kholia/PDX-Plus-Plus/screenshots/SA-On-Random-Wire-In-Balcony-Screenshot_2022-12-01_08-14-44.png

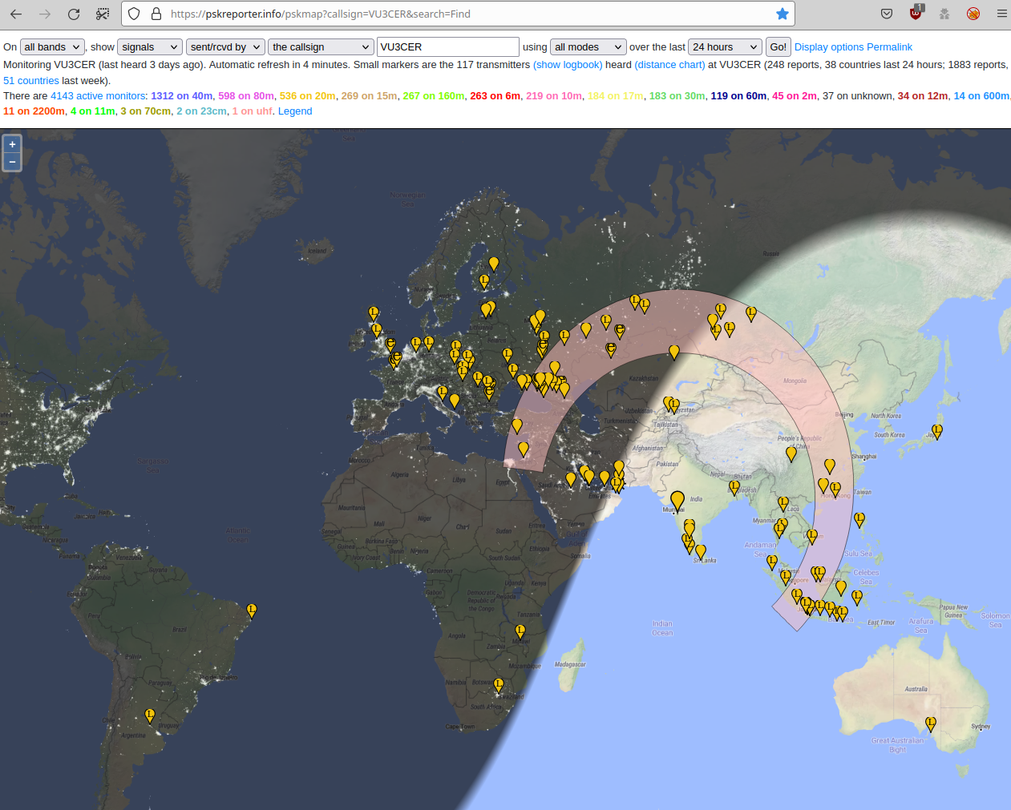
screenshots/SA-On-Random-Wire-In-Balcony-Screenshot_2022-12-01_08-14-44.png
