kholia/PDX-Plus-Plus/screenshots/Screenshot_2022-11-28_12-23-08.png

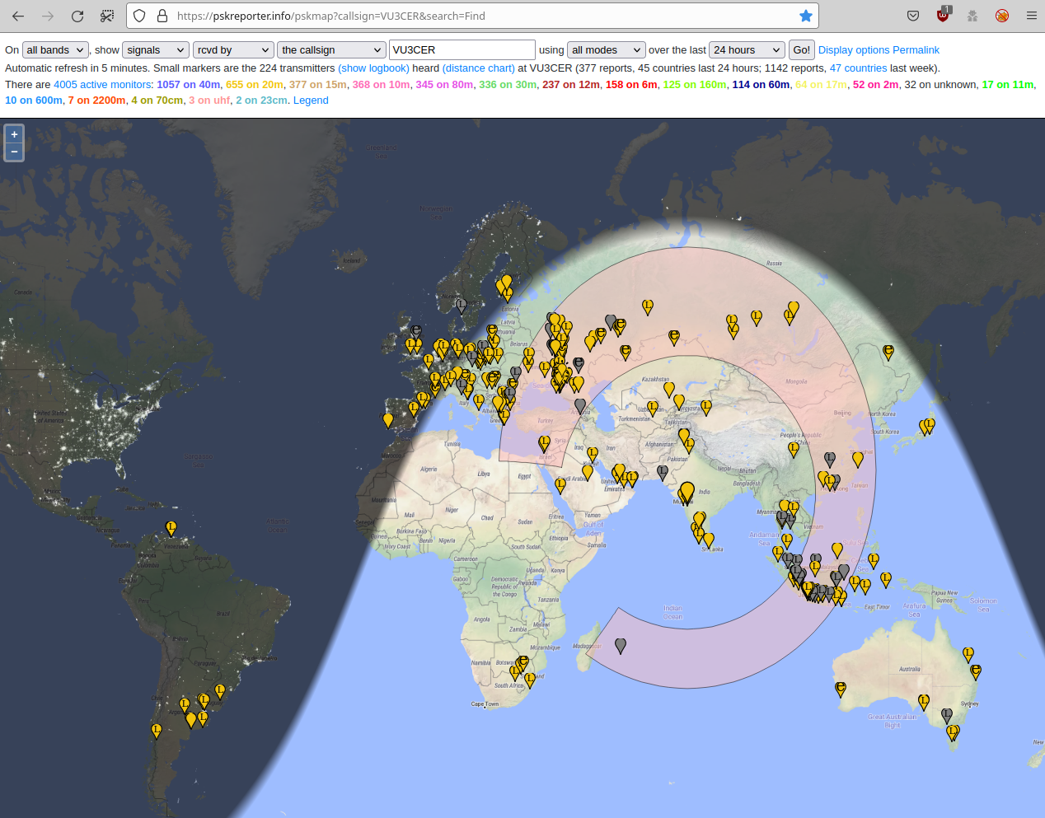
screenshots/Screenshot_2022-11-28_12-23-08.png
