kholia/PDX-Plus-Plus/screenshots/Screenshot_2022-11-28_17-31-01.png

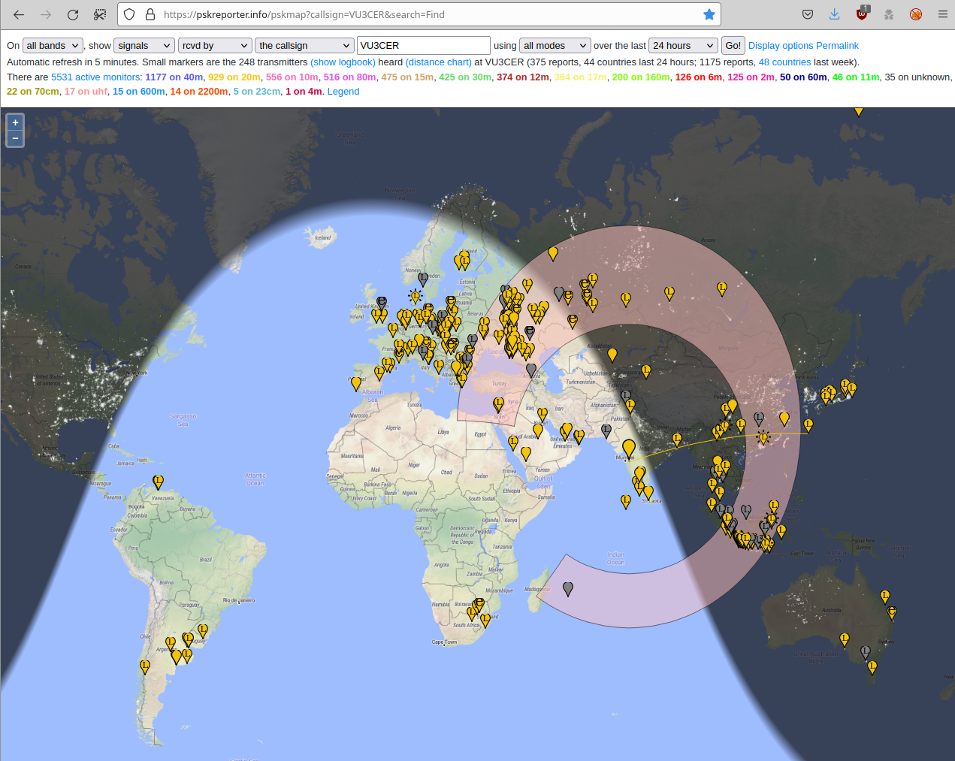
screenshots/Screenshot_2022-11-28_17-31-01.png
