kholia/PDX-Plus-Plus/screenshots/Screenshot_2022-11-28_20-12-07.png

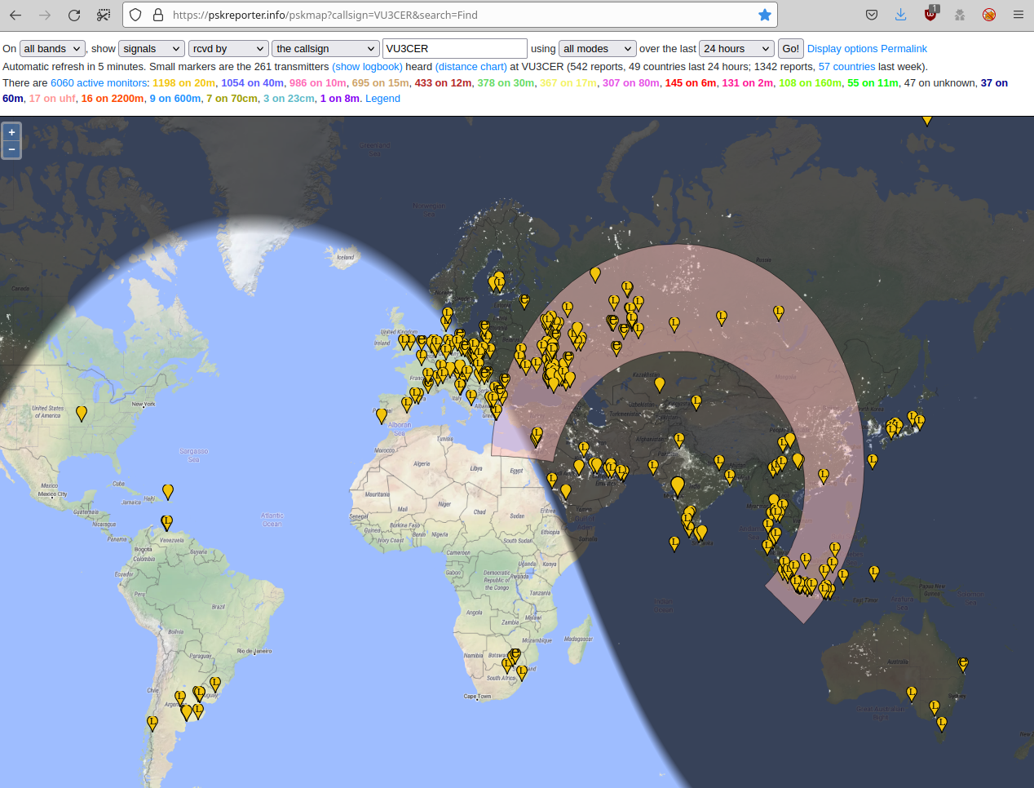
screenshots/Screenshot_2022-11-28_20-12-07.png
