kholia/PDX-Plus-Plus/screenshots/Screenshot_2022-11-28_22-39-48.png

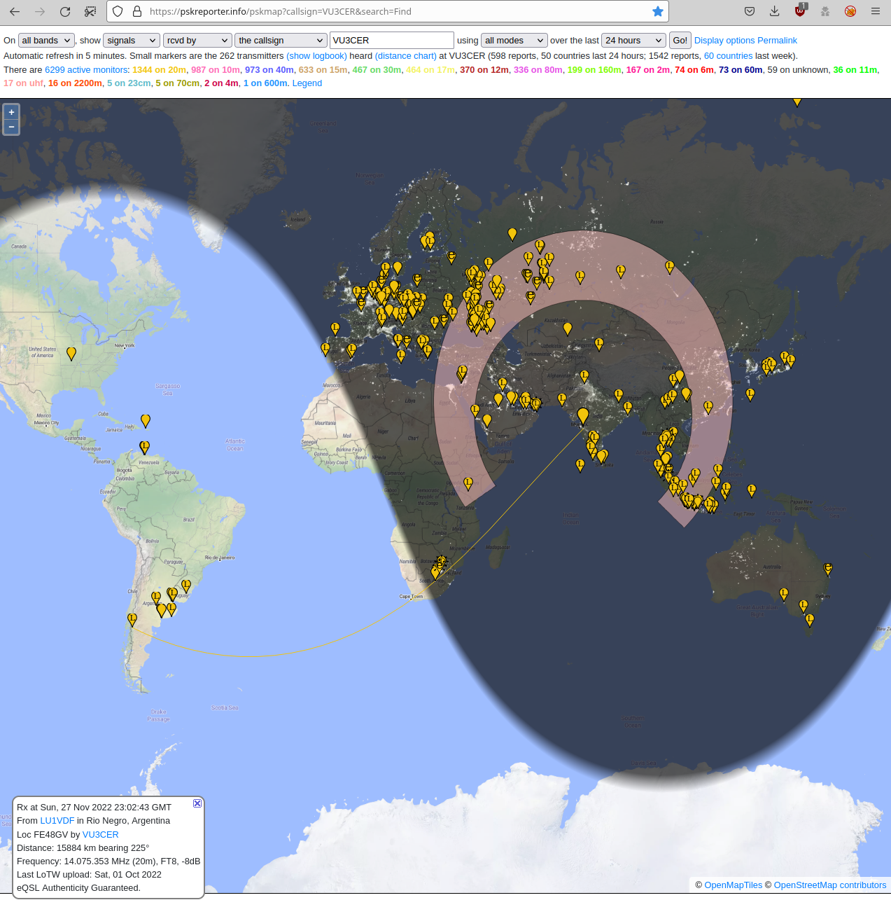
screenshots/Screenshot_2022-11-28_22-39-48.png
