kholia/PDX-Plus-Plus/screenshots/Screenshot_2022-11-29_09-19-55.png

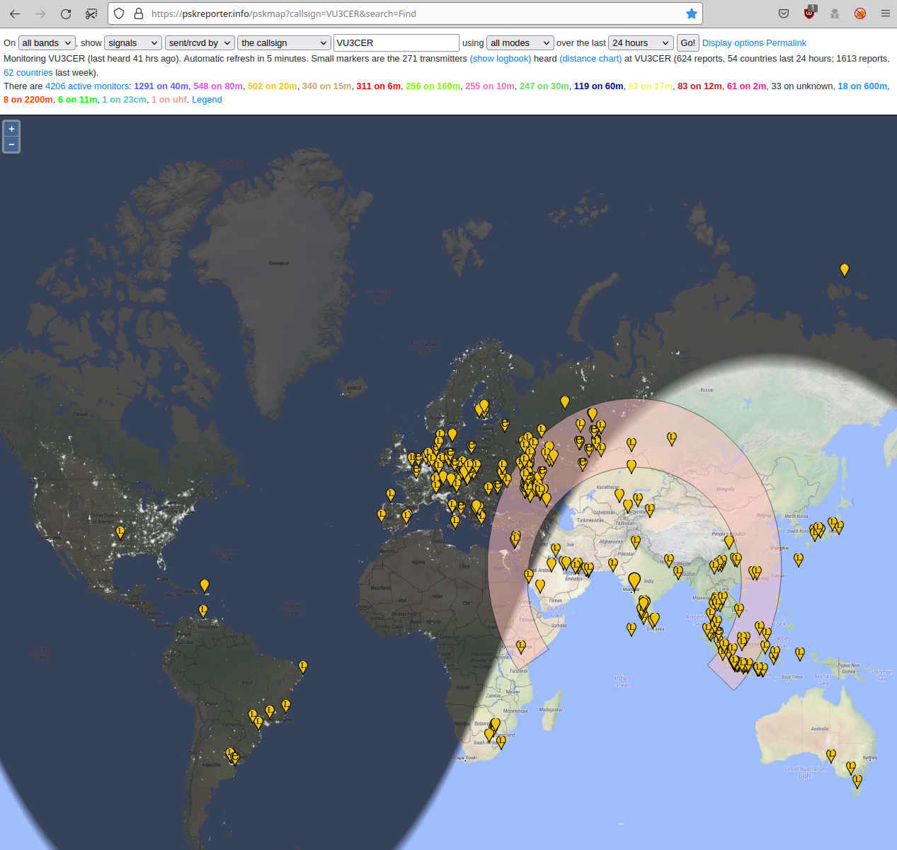
screenshots/Screenshot_2022-11-29_09-19-55.png
