kholia/PDX-Plus-Plus/screenshots/Screenshot_2022-11-29_20-50-16.png

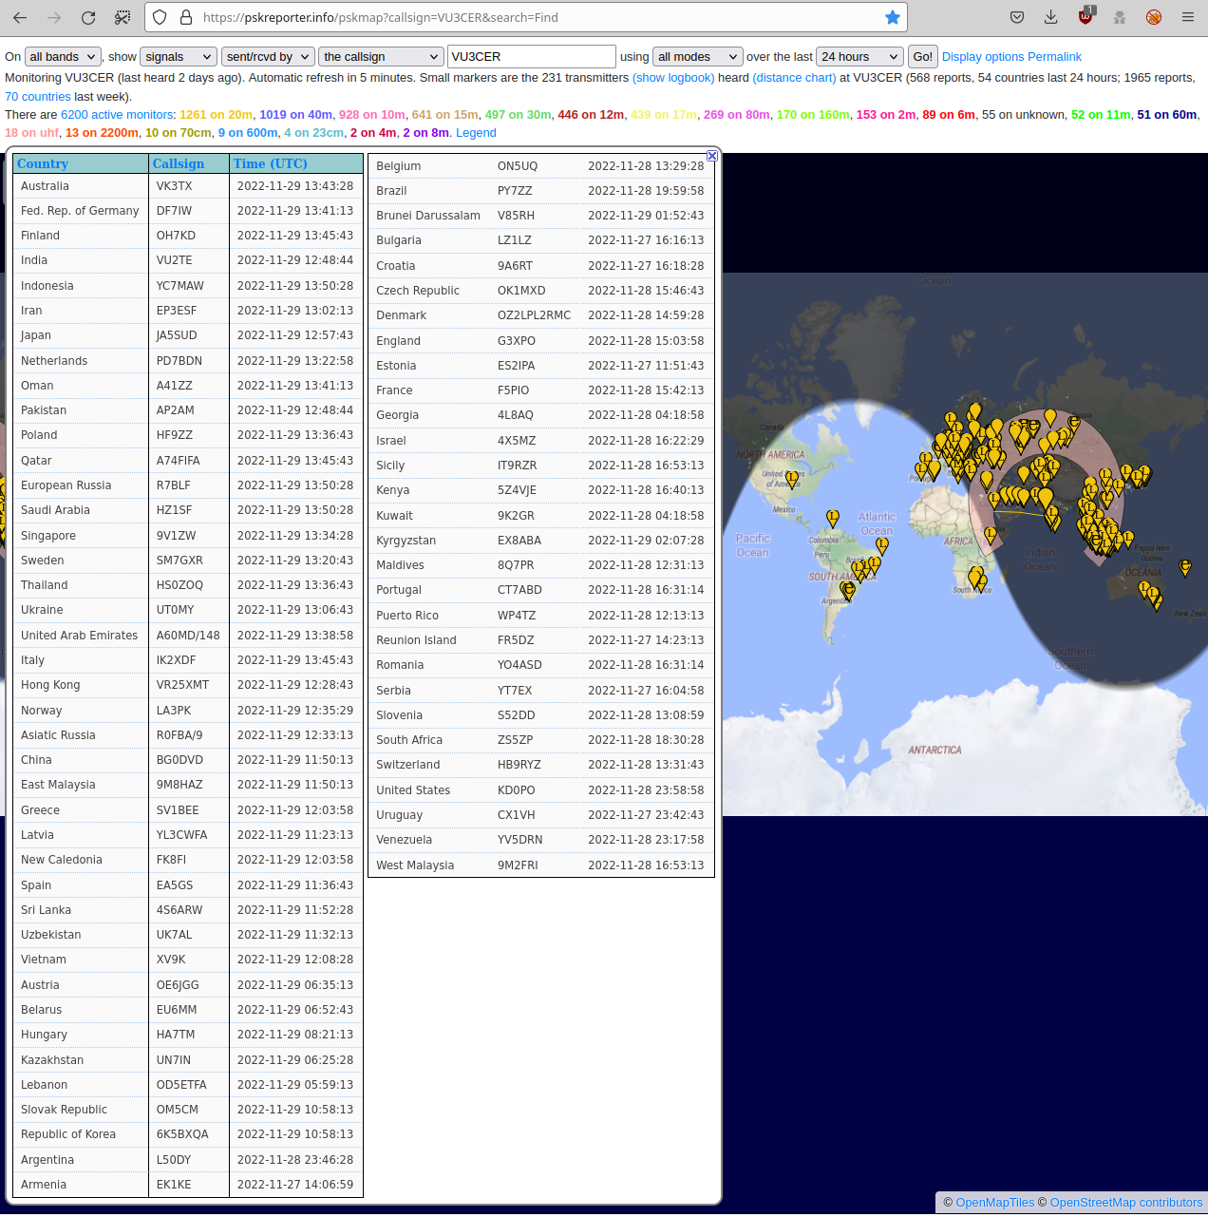
screenshots/Screenshot_2022-11-29_20-50-16.png
