kholia/PDX-Plus-Plus/simulations/BCI-Filter/Screenshot_2022-10-23_14-13-40.png

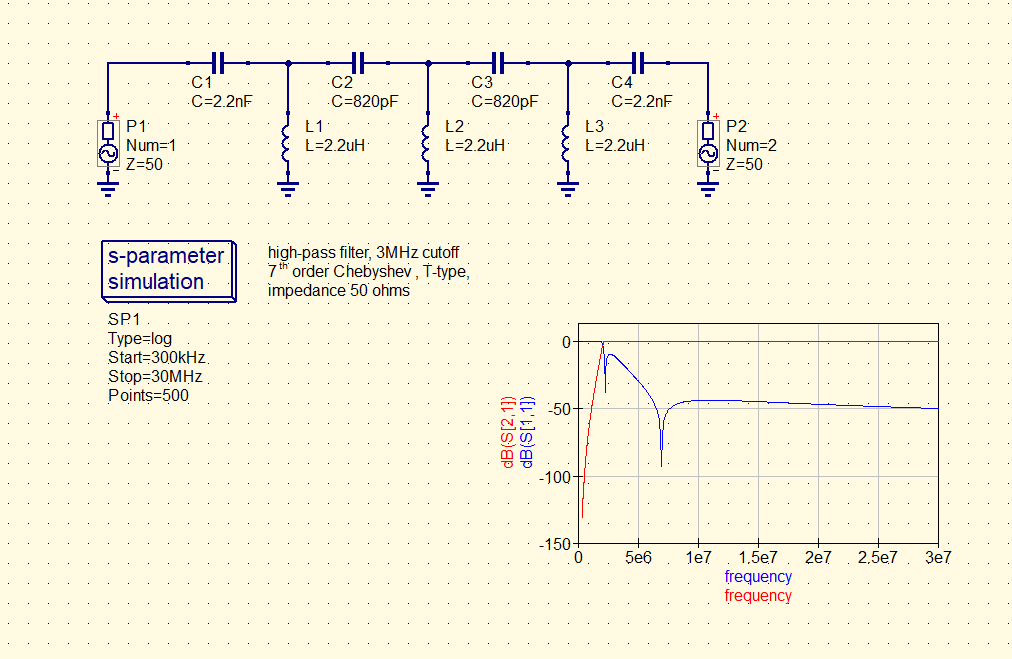
simulations/BCI-Filter/Screenshot_2022-10-23_14-13-40.png
