kholia/PDX-Plus-Plus/simulations/Screenshot_2022-10-13_21-20-04.png

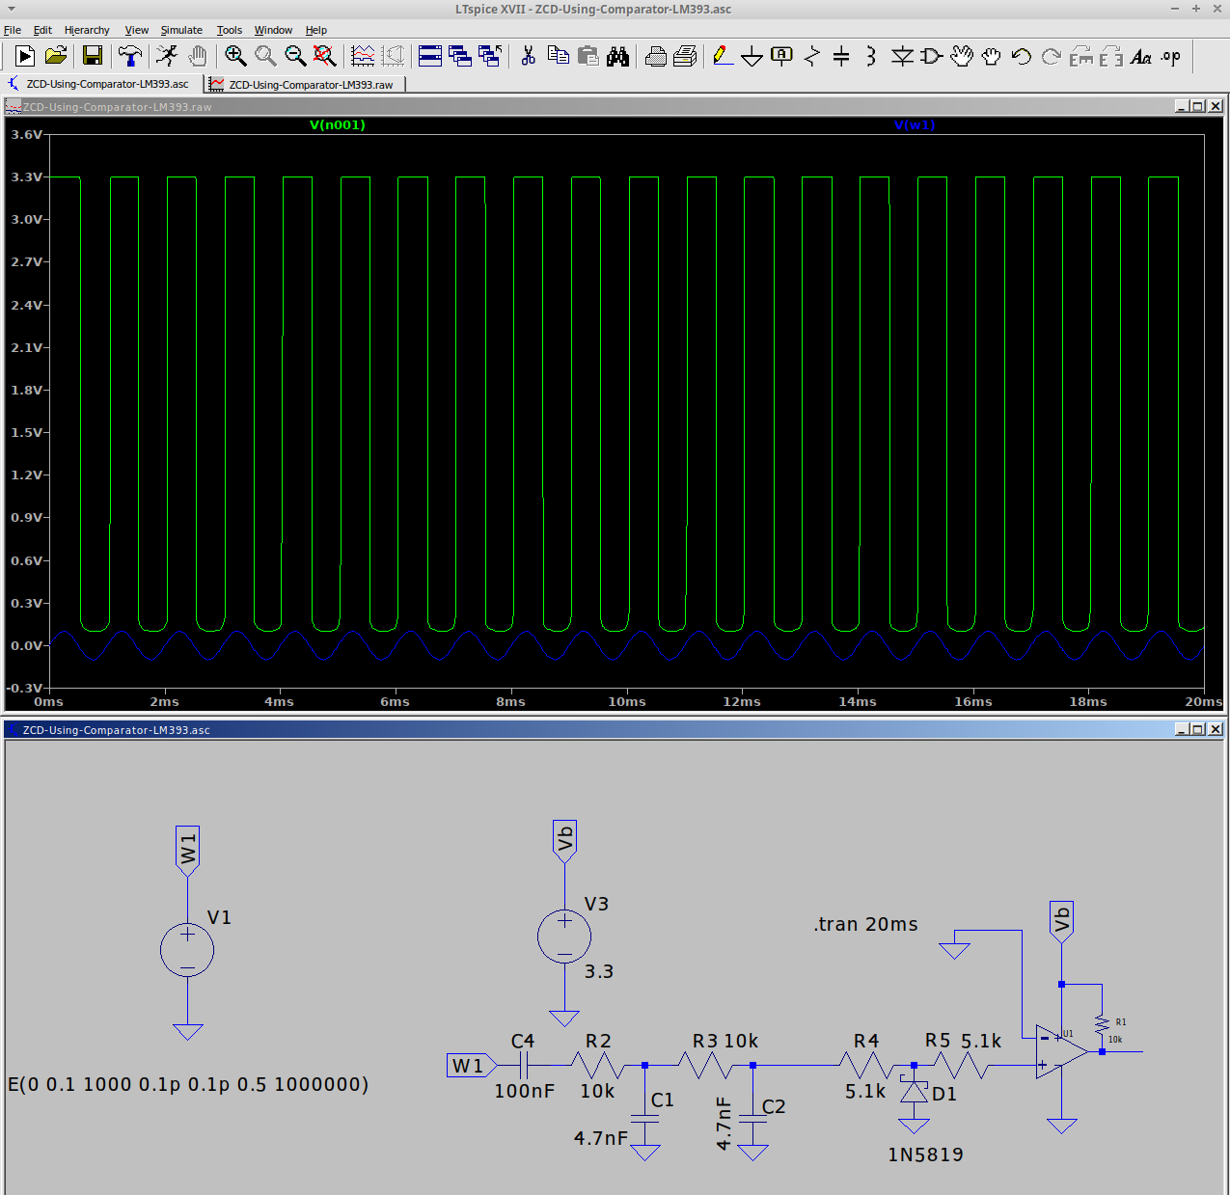
simulations/Screenshot_2022-10-13_21-20-04.png
