kholia/PDX-Plus-Plus/simulations/Screenshot_2022-10-19_10-21-50.png

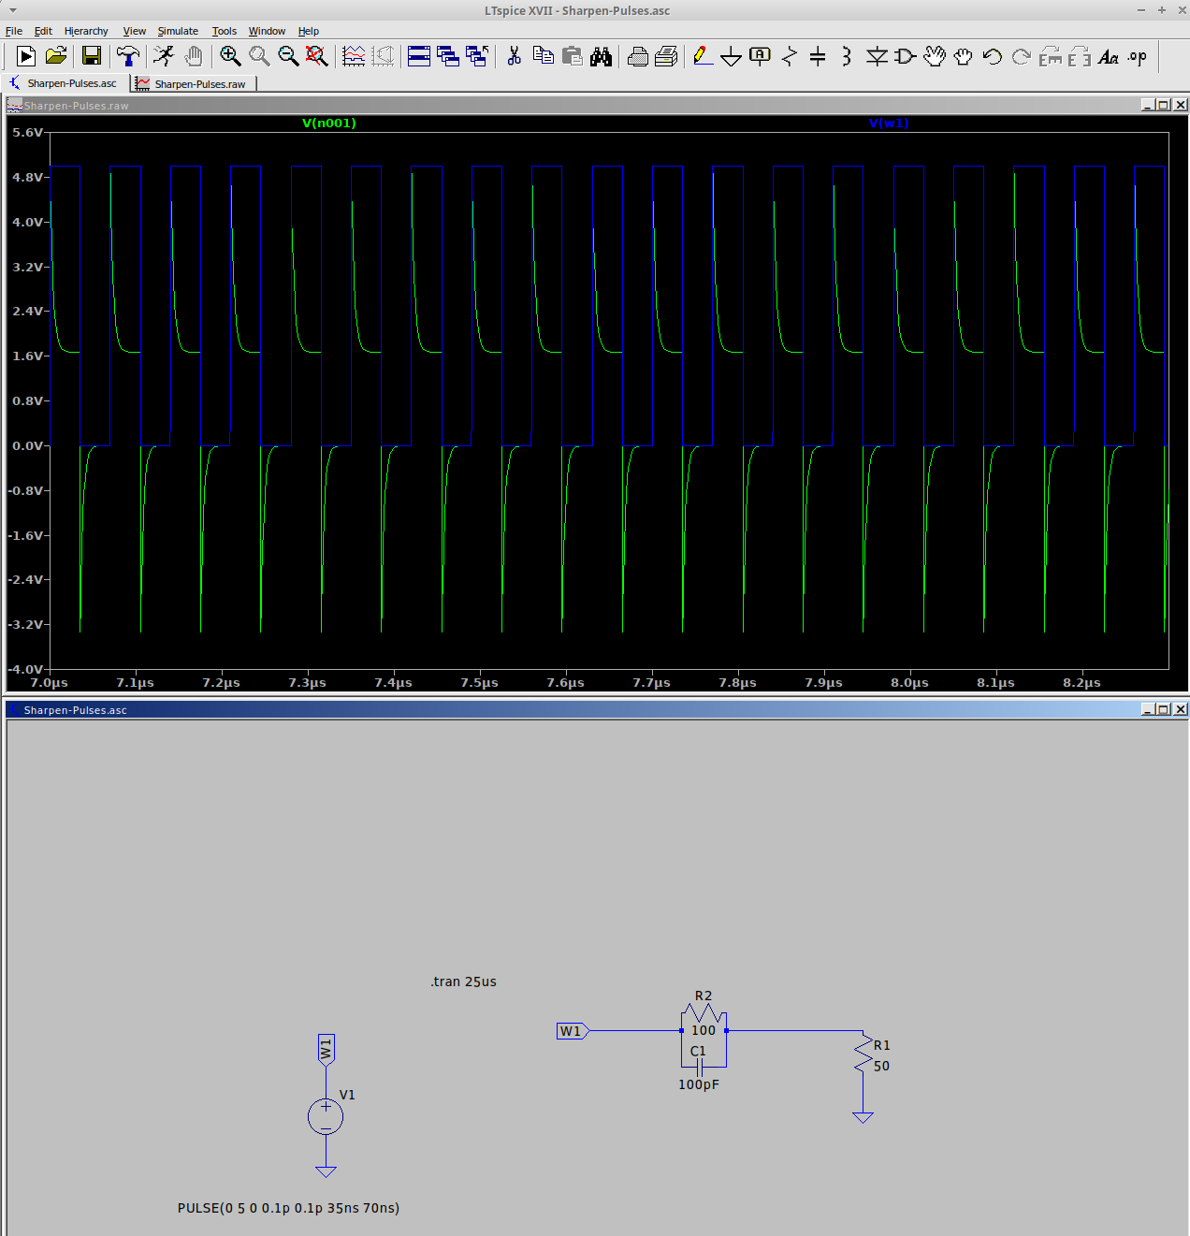
simulations/Screenshot_2022-10-19_10-21-50.png
