kholia/PDX-Plus-Plus/simulations/Screenshot_2022-11-19_09-56-32.png

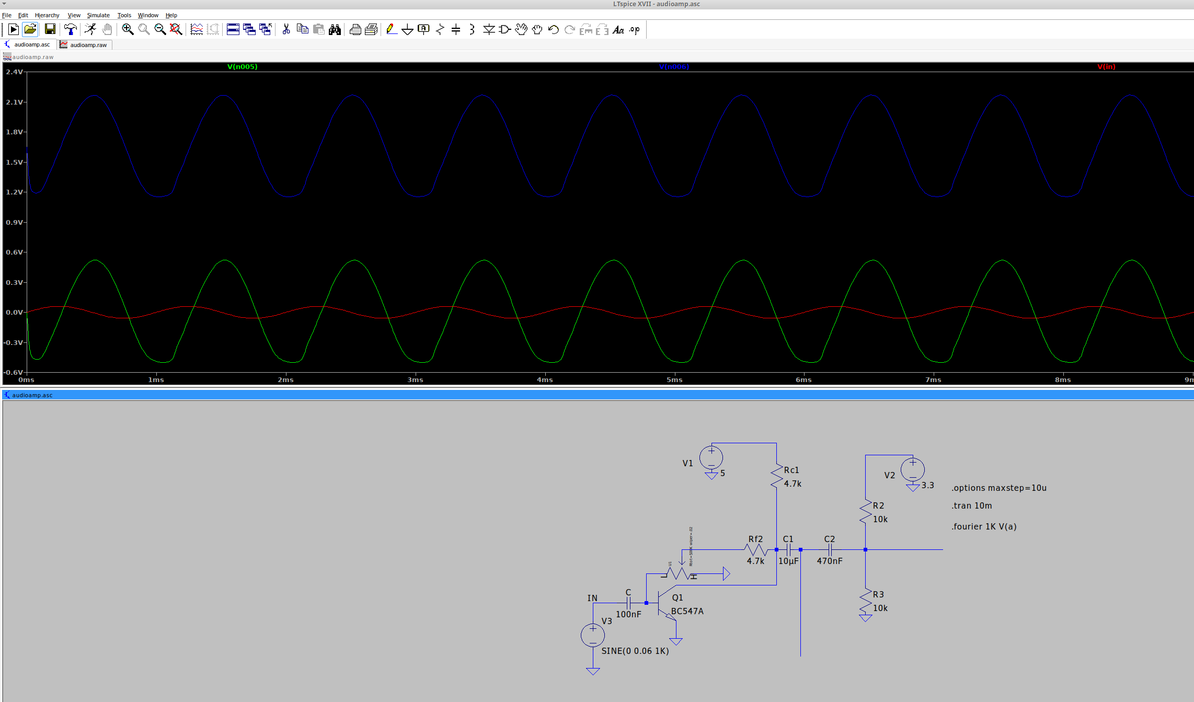
simulations/Screenshot_2022-11-19_09-56-32.png
