kholia/PDX-Plus-Plus/PDX_THD_V1.00/ADX PDF Files/ADX component layout.jpg

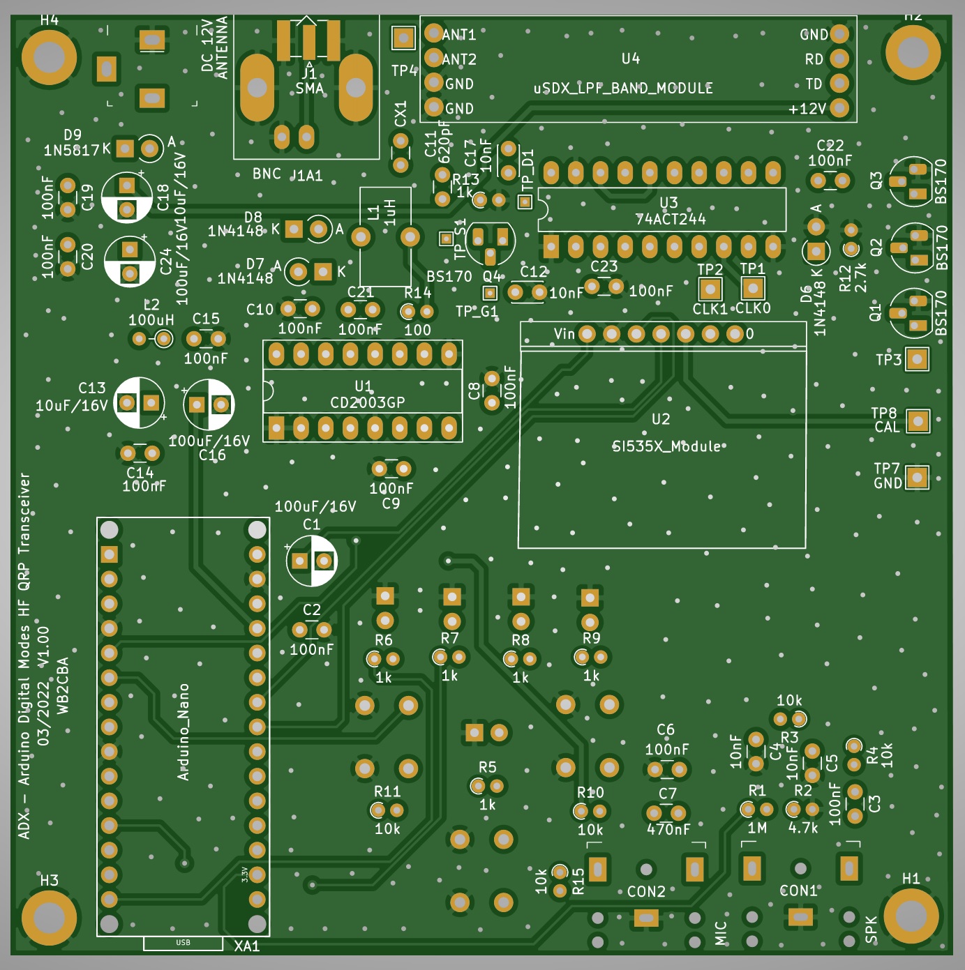
PDX_THD_V1.00/ADX PDF Files/ADX component layout.jpg
