kholia/PDX-Plus-Plus/PDX_THD_V1.00/ADX test component layout.jpg

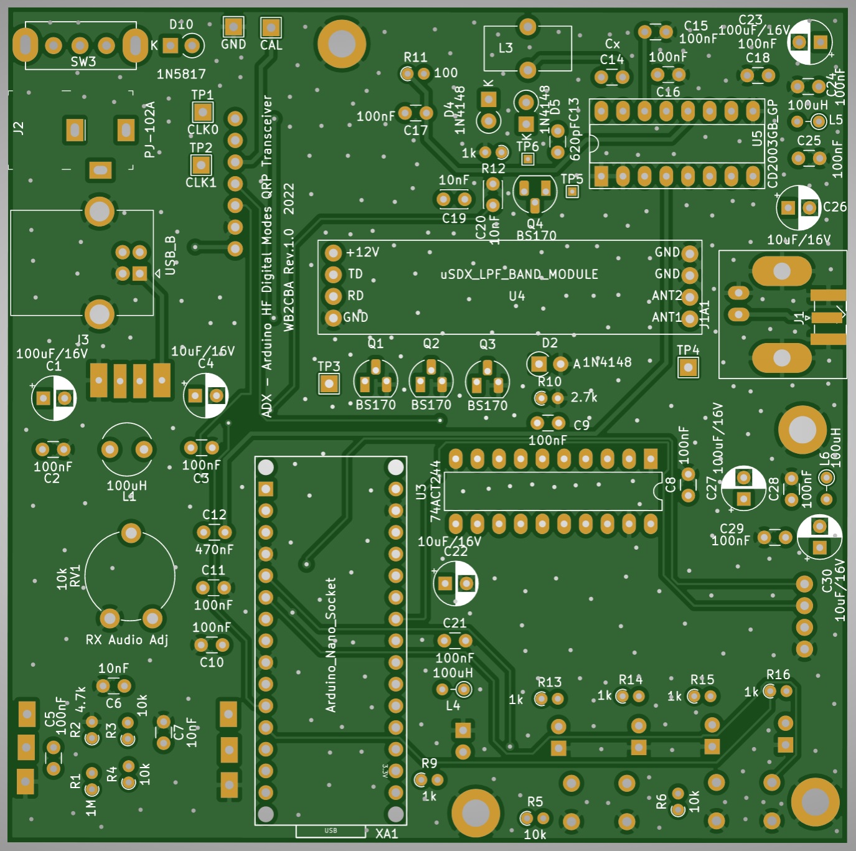
PDX_THD_V1.00/ADX test component layout.jpg
