kholia/PDX-Plus-Plus/PDX_THD_V1.00/ADX PDF Files/ADX solder side layout.jpg

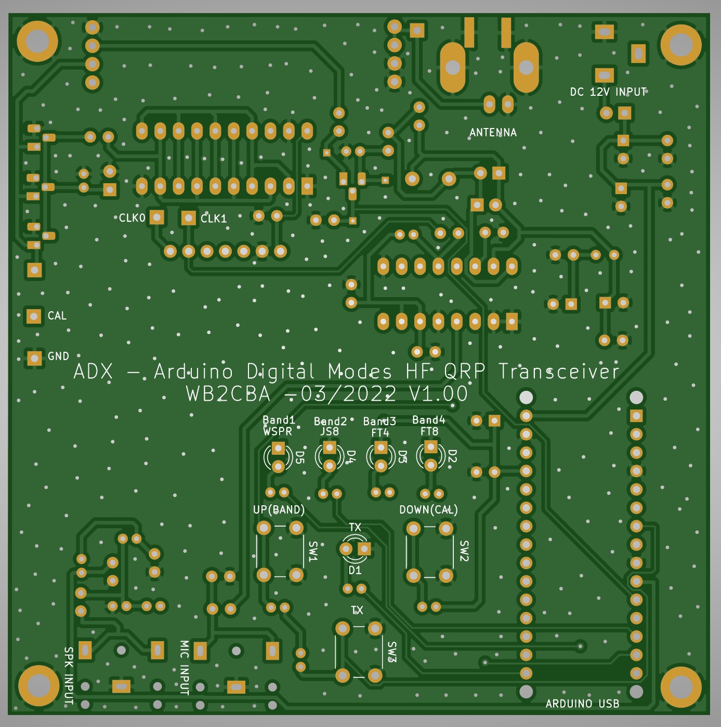
PDX_THD_V1.00/ADX PDF Files/ADX solder side layout.jpg
