kholia/PDX-Plus-Plus/PDX_THD_V1.00/ADX test solder side layout.jpg

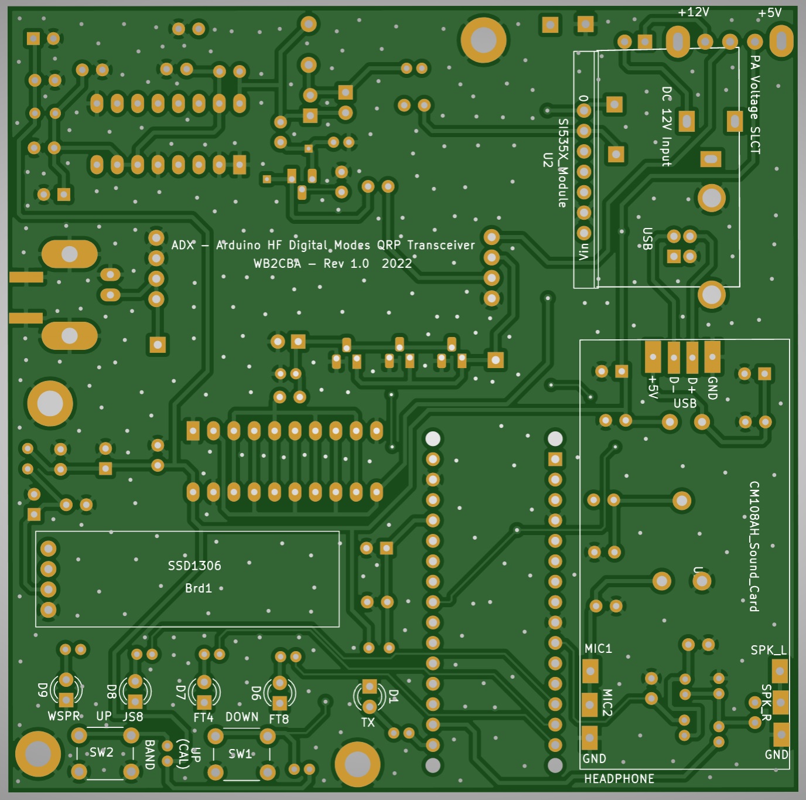
PDX_THD_V1.00/ADX test solder side layout.jpg
