kholia/PDX-Plus-Plus/screenshots/RX-Performance-Screenshot_2022-11-28_08-41-41.png

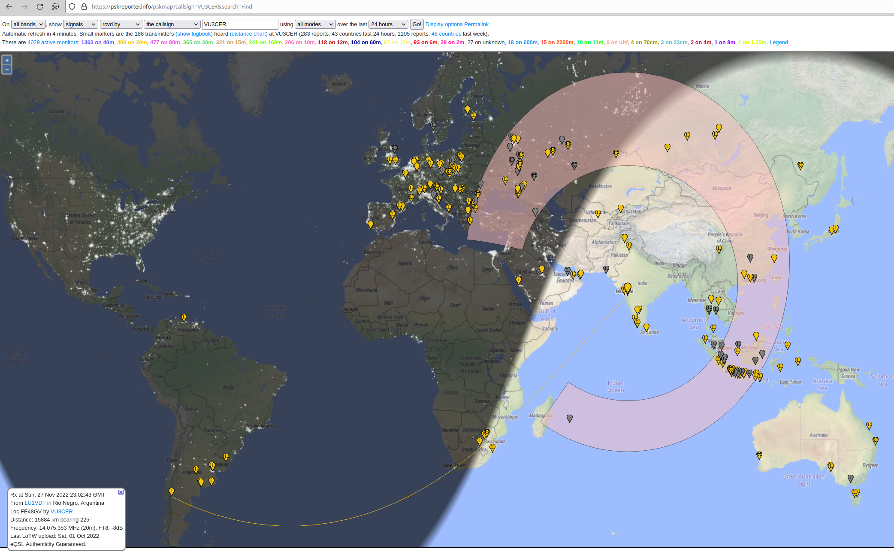
screenshots/RX-Performance-Screenshot_2022-11-28_08-41-41.png
