kholia/PDX-Plus-Plus/simulations/audioamp.asc

C1: cap; 10µF
C2: cap; 470nF
C: cap; 100nF
Q1: npn; BC547A
R2: res; 10k
R3: res; 10k
Rc1: res; 4.7k
Rf2: res; 4.7k
U1: potentiometer; Rtot=500K wiper=.02
V1: VOLTAGE; 5
V2: VOLTAGE; 3.3
V3: voltage; SINE(0 0.06 1K)
Named nets: 0, IN
.tran 10m
.options maxstep=10u
.fourier 1K V(a)
