kholia/PDX-Plus-Plus/simulations/Sharpen-Pulses.asc

C1: cap; 100pF
R1: res; 50
R2: res; 100
V1: voltage; PULSE(0 5 0 0.1p 0.1p 35ns 70ns)
Named nets: W1, 0
.tran 25us
