kholia/PDX-Plus-Plus/simulations/ZCD-Using-Comparator-LM393.asc

C1: cap; 4.7nF
C2: cap; 4.7nF
C4: cap; 100nF
D1: schottky; 1N5819
R1: res-; 10k
R2: res; 10k
R3: res; 10k
R4: res; 5.1k
R5: res; 5.1k
U1: lm393
V1: voltage; SINE(0 0.1 1000 0.1p 0.1p 0.5 1000000)
V3: voltage; 3.3
Named nets: W1, 0, Vb
.tran 20ms
