kholia/PDX-Plus-Plus/firmware_v0.01/credits.h

//*=*=*=*=*=*=*=*=*=*=*=*=*=*=*=*=*=*=*=*=*=*=*=*=*=*=*=*=*=*=*=*=*=*=*=*=*=*=*=*=*=*=*=*=*=*=*=*=*=*=*=**=*=*
//*                           PDX - PICO based DIGITAL MODES 4 BAND HF TRANSCEIVER                           *
//*=*=*=*=*=*=*=*=*=*=*=*=*=*=*=*=*=*=*=*=*=*=*=*=*=*=*=*=*=*=*=*=*=*=*=*=*=*=*=*=*=*=*=*=*=*=*=*=*=*=*=**=*=*
// Firmware Version 2.0
//
// Barb (Barbaros ASUROGLU) - WB2CBA - 2022
// Dhiru (Dhiru Kholia)     - VU3CER - 2022
// Pedro (Pedro Colla)      - LU7DZ  - 2022
